adereth/dactyl-keyboard/resources/prototype.jpg

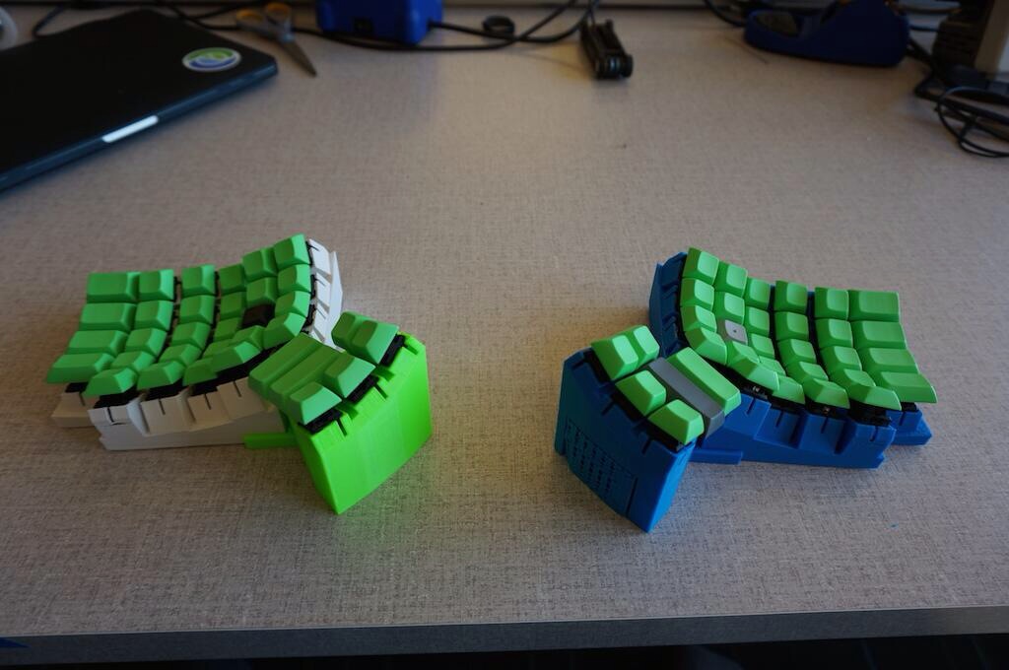
resources/prototype.jpg
